milanvidakovic/FPGAComputer32/chars.v

//////////////////////////////////////////////////////////////////////////////////
// Company: 
// Engineer: 
// 
// Character generator holding 8x8 character images.
// Input char is a 4-bit character number representing:
// 0, 1, 2, 3, 4, 5, 6, 7, 8, 9, B, F, i, z, <blank>
// Input rownum is the desired row of the pixel image
// Output pixels is the 8 pixel row, pixels[7] is leftmost.
// Original font from https://github.com/dhepper/font8x8/blob/master/font8x8_basic.h
module chars(
    input [7:0] char,
    input [2:0] rownum,
    output reg [7:0] pixels
    );

always @(*)
  case ({char, rownum})

    11'b00110000000: pixels = 8'b01111100; //  XXXXX  
    11'b00110000001: pixels = 8'b11000110; // XX   XX 
    11'b00110000010: pixels = 8'b11001110; // XX  XXX 
    11'b00110000011: pixels = 8'b11011110; // XX XXXX 
    11'b00110000100: pixels = 8'b11110110; // XXXX XX 
    11'b00110000101: pixels = 8'b11100110; // XXX  XX 
    11'b00110000110: pixels = 8'b01111100; //  XXXXX  
    11'b00110000111: pixels = 8'b00000000; //         

    11'b00110001000: pixels = 8'b00110000; //   XX    
    11'b00110001001: pixels = 8'b01110000; //  XXX    
    11'b00110001010: pixels = 8'b00110000; //   XX    
    11'b00110001011: pixels = 8'b00110000; //   XX    
    11'b00110001100: pixels = 8'b00110000; //   XX    
    11'b00110001101: pixels = 8'b00110000; //   XX    
    11'b00110001110: pixels = 8'b11111100; // XXXXXX  
    11'b00110001111: pixels = 8'b00000000; //         

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
    11'b01111100011: pixels = 8'b00000000; //         
    11'b01111100100: pixels = 8'b00011000; //    XX   
    11'b01111100101: pixels = 8'b00011000; //    XX   
    11'b01111100110: pixels = 8'b00011000; //    XX   
    11'b01111100111: pixels = 8'b00000000; //         

    11'b10111101000: pixels = 8'b11111111; // XXXXXXX
    11'b10111101001: pixels = 8'b11111111; // XXXXXXX
    11'b10111101010: pixels = 8'b11111111; // XXXXXXX
    11'b10111101011: pixels = 8'b11111111; // XXXXXXX
    11'b10111101100: pixels = 8'b11111111; // XXXXXXX
    11'b10111101101: pixels = 8'b11111111; // XXXXXXX
    11'b10111101110: pixels = 8'b11111111; // XXXXXXX
    11'b10111101111: pixels = 8'b11111111; // XXXXXXX
	 
    11'b01100000000: pixels = 8'b01100000; //  XX       
    11'b01100000001: pixels = 8'b00110000; //   XX     
    11'b01100000010: pixels = 8'b00000000; //         
    11'b01100000011: pixels = 8'b00000000; //         
    11'b01100000100: pixels = 8'b00000000; //         
    11'b01100000101: pixels = 8'b00000000; //         
    11'b01100000110: pixels = 8'b00000000; //         
    11'b01100000111: pixels = 8'b00000000; //         

    
    default: pixels <= 8'b00000000;
  endcase
endmodule 
