milanvidakovic/FPGAComputer32/fpmul_inst.v

fpmul	fpmul_inst (
	.clk_en ( clk_en_sig ),
	.clock ( clock_sig ),
	.dataa ( dataa_sig ),
	.datab ( datab_sig ),
	.overflow ( overflow_sig ),
	.result ( result_sig ),
	.underflow ( underflow_sig )
	);
